ale-kincaid/Light_Sensor/Core/Inc/battery.h

/*
 * battery.h
 *
 *  Created on: Feb 24, 2026
 *      Author: Ale K. & Ben G.
 */

#ifndef INC_BATTERY_H_
#define INC_BATTERY_H_

// Read and print the system ext. voltage.
void battery_read_command(char *arguments);

#endif /* INC_BATTERY_H_ */
