ale-kincaid/Light_Sensor/Core/Inc/interrupt.h

/* interrupt.h
 * Description:
 *
 * Author: Bryce Himebaugh
 * Contact: bhimebau@indiana.edu
 * Date: 06.21.2019
 * Copyright (C) 2019
 *
 */

uint32_t disable(void);
void restore(uint32_t);
void enable(void);
