ale-kincaid/Light_Sensor/Core/Inc/queue.h

/* queue.h ---
 *
 * Filename: queue.h
 * Description:
 * Author: Bryce Himebaugh
 * Maintainer:
 * Created: Thu Feb  7 19:47:41 2013 (-0500)
 * Version:
 * Last-Updated:
 *           By:
 *     Update #: 0
 * URL:
 * Doc URL:
 * Keywords:
 * Compatibility:
 *
 */

/* Commentary:
 *
 *
 *
 */

/* Change Log:
 *
 *
 */

/*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
 * You should have received a copy of the GNU General Public License
 * along with this program; see the file COPYING.  If not, write to
 * the Free Software Foundation, Inc., 51 Franklin Street, Fifth
 * Floor, Boston, MA 02110-1301, USA.
 */

/* Code: */
#include "stm32l4xx.h"

#define QUEUE_SIZE 32

#ifndef QUEUE_H
#define QUEUE_H

typedef struct queue {
  int head;
  int tail;
  uint8_t buffer[QUEUE_SIZE];
} queue_t;

#endif


void init_queue(queue_t *);
int enqueue(queue_t *, uint8_t);
uint8_t dequeue(queue_t *);
int queue_empty(queue_t *);

/* queue.h ends here */
