ale-kincaid/Light_Sensor/Core/Inc/temperature.h

/*
 * temperature.h
 *
 *  Created on: Feb 22, 2026
 *      Author: Ale K. & Ben G.
 */

#ifndef INC_TEMPERATURE_H_
#define INC_TEMPERATURE_H_

// Read and print the temperature of the chip in C.
void temp_read_command(char *arguments);

#endif /* INC_TEMPERATURE_H_ */
