ale-kincaid/Light_Sensor/Core/Inc/sample.h

/*
 * sample.h
 *
 *  Created on: Mar 1, 2026
 *      Author: Ale K. & Ben G.
 */

#ifndef INC_SAMPLE_H_
#define INC_SAMPLE_H_

void sample(void);
void sample_command(char *arguments);
void log_func(const char *message);
void data_command(char *arguments);

#endif /* INC_SAMPLE_H_ */
